Azeal542/Library-IMS/API.py

"""
To do:
- Audit updateDevice in Assets.py
- Audit auditAsset in Assets.py
- Audit getAuditDue in Assets.py
- Audit getAuditOverdue in Assets.py


"""

import json
from snipeit import Assets, Users
import os
from dotenv import load_dotenv

load_dotenv()

token = os.getenv('SNIPE_IT_API_KEY')
server= os.getenv('SNIPE_IT_BASE_URL')

def get_assets():
    A = Assets()
    r = A.get(server, token, limit=None, order='asc', offset=None)
    return r

def check_in_asset(assetID):
    A = Assets()
    r = A.checkInAsset(server, token, assetID, note=None, locationID=None)
    return r

def get_asset(AssetTAG):
    A = Assets()
    r = A.getDetailsByTag(server, token, AssetTAG)
    return r

def check_out_asset(assetID, userID):
    A = Assets()
    r = A.checkOutAsset(server, token, assetID, userID, note=None, locationID=None)
    return r
    

def search_assets(keyword):
    A = Assets()
    r = A.search(server, token, limit=None, order='asc', keyword=keyword, offset=None)
    return r

def get_asset_by_model(modelID):
    A = Assets()
    r = A.getAssetsByModel(server, token, modelID, limit=None, order='asc', offset=None)
    return r

def get_asset_by_category(categoryID):
    A = Assets()
    r = A.getAssetsByCategory(server, token, categoryID, limit=None, order='asc', offset=None)
    return r

def get_asset_by_manufacturer(manufacturerID):
    A = Assets()
    r = A.getAssetsByManufacturer(server, token, manufacturerID, limit=None, order='asc', offset=None)
    return r

def get_assets_by_company(companyID):
    A = Assets()
    r = A.getAssetsByCompany(server, token, companyID, limit=None, order='asc', offset=None)
    return r

def get_asset_by_location(locationID):
    A = Assets()
    r = A.getAssetsByLocation(server, token, locationID, limit=None, order='asc', offset=None)
    return r

def get_asset_by_status(statusID):
    A = Assets()
    r = A.getAssetsByStatus(server, token, statusID, limit=None, order='asc', offset=None)
    return r

def get_asset_by_status_label(statusLabel):
    A = Assets()
    r = A.getAssetsByStatusLabel(server, token, statusLabel, limit=None, order='asc', offset=None)
    return r

def get_details_by_id(assetID):
    A = Assets()
    r = A.getDetailsByID(server, token, assetID)
    return r

def get_details_by_tag(tag):
    A = Assets()
    r = A.getDetailsByTag(server, token, tag)
    return r

def get_details_by_serial(serial):
    A = Assets()
    r = A.getDetailsBySerial(server, token, serial)
    return r

def create_asset(asset_tag, status_id, model_id, name, serial):
    A = Assets()
    r = A.create(server, token, asset_tag, status_id, model_id, name, serial)
    return r

def get_id(asset_tag):
    A = Assets()
    r = A.getID(server, token, asset_tag)
    return r

def delete_asset(assetID):
    A = Assets()
    r = A.delete(server, token, assetID)
    return r

def get_ID_by_EmployeeID(employeeID):
    U = Users()
    r = U.getIDByEmployeeID(server, token, employeeID)
    return r
def get_Full_Name_By_Employee_ID(employeeID):
    U = Users()
    r = U.getFullNameByEmployeeID(server, token, employeeID)
    return r

def get_Data_By_Serial(assetID):
    A = Assets()
    r = A.getDataBySerial(server, token, assetID)
    return r
    #return r

def get_User_By_Email(email):
    U = Users()
    r = U.getUserbyEmail(server, token, email)
    #print(r)
    return r

def create_user(first_name, username, password, last_name, email, employee_num):
    U = Users()
    r = U.create(server, token, first_name, username, password, last_name, email, employee_num)
    return r


#create_user("Test", "testuser123", "TestPassword!23", "User", "testuser123@kfheadstart.org", 10)

#get_User_By_Email("wendy.mendes@kfheadstart.org")

#check_out_asset(1, 1)
#get_asset("asdf1234")
#check_in_asset(1)
#get_assets()
#search_assets("1234")
#get_asset_by_model("book")
#get_asset_by_category("2")
#get_asset_by_manufacturer("")
#get_assets_by_company("")
#get_asset_by_location("")
#get_asset_by_status("1")
#get_asset_by_status_label("")
#get_details_by_id("1")
#get_details_by_tag("asdf1234")
#get_details_by_serial("1234")
#create_asset("testtag1234", 2, 1, "Test Asset")
#get_id("testtag1234")
#delete_asset("2")
#get_ID_by_EmployeeID("12341234")
#get_Full_Name_By_Employee_ID("12341234")
#list = ["123443121", "1234"]
#for each in list:
#    get_Name_By_Serial(each)
#get_Data_By_Serial("1234")
# returns ('null', 'asdf1234')
#print(json.loads(get_details_by_tag("asdf1234"))['serial'])
#each = "1"
#result = check_in_asset(each)
#if json.loads(result)['status'] != 'success':
#    tagdetails = get_details_by_tag(json.loads(result)['payload']['asset_tag']).decode('utf-8')
#    serialdetails = json.loads(tagdetails)['serial']
#    NameSerial = get_Data_By_Serial(serialdetails)
#    print("Error checking in asset:", "Error checking in asset " + NameSerial[0] + " is already checked in.")
#check_in_asset("3")
